ethantruman/cheepy_pi/RP2040_firmware/keyboard_rtos/output_frames/reze_frame_006.png

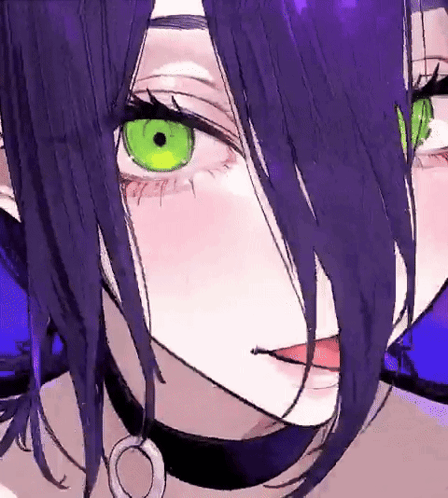
RP2040_firmware/keyboard_rtos/output_frames/reze_frame_006.png
