ethantruman/cheepy_pi/RP2040_firmware/keyboard_rtos/image_data.h

// File tự động tạo bởi Python Script
// Kích thước mỗi ảnh: 71x64 (RGB565 Big-Endian)
#ifndef IMAGE_DATA_H
#define IMAGE_DATA_H

#include <Arduino.h>

#define IMAGE_WIDTH 71
#define IMAGE_HEIGHT 64
#define IMAGE_PIXEL_COUNT 4544
#define TOTAL_IMAGES 6

// Image: reze_frame_001.png
const uint16_t reze_frame_001[4544] PROGMEM = {
    0x414B, 0x416D, 0x392C, 0x412C, 0x416D, 0x496D, 0x518E, 0x518F, 0x496E, 0x59B0, 0x410D, 0x9C54,
    0xFFFF, 0xFF9E, 0xFF9E, 0xFFFF, 0xA4B4, 0x38EB, 0x414C, 0x412C, 0x392C, 0x392C, 0x412D, 0x414D,
    0x496F, 0x494F, 0x6195, 0x81DB, 0x6996, 0x81FB, 0x9A5F, 0x923E, 0x8A1C, 0x925E, 0x925F, 0x923E,
    0x923F, 0x923D, 0x923E, 0x921E, 0x923E, 0x71B7, 0x6174, 0x6996, 0x5972, 0x5151, 0x5151, 0x5151,
    0x59B1, 0x72B1, 0xA476, 0xFFBE, 0xDE7A, 0xFFFF, 0xD5F8, 0x59CE, 0x496F, 0x496F, 0x496E, 0x516F,
    0x498E, 0x414C, 0x414C, 0x496D, 0x496D, 0x498E, 0x414D, 0x414C, 0x414C, 0x414C, 0x414C, 0x414C,
    0x416C, 0x392B, 0x414B, 0x498D, 0x498D, 0x51AF, 0x518F, 0x496E, 0x51AF, 0x496D, 0xDE9B, 0xFFFF,
    0xFFBE, 0xFFBE, 0xFFFF, 0xE6BB, 0x416C, 0x414C, 0x414C, 0x414D, 0x414C, 0x412C, 0x414D, 0x494E,
    0x496F, 0x494F, 0x5973, 0x6175, 0x71B7, 0x923F, 0x923F, 0x81FB, 0x923E, 0x8A1C, 0x71B7, 0x81FC,
    0x8A1C, 0x925E, 0x923E, 0x921D, 0x6996, 0x6174, 0x6174, 0x5972, 0x5171, 0x5151, 0x5151, 0x59D1,
    0x7AB2, 0xB4F7, 0xFFFF, 0xE69A, 0xFFFF, 0xF71C, 0x8332, 0x414D, 0x496E, 0x496E, 0x498E, 0x498E,
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
};

// Mảng chứa con trỏ tới tất cả các ảnh để duyệt vòng lặp for
const uint16_t* const all_images[TOTAL_IMAGES] PROGMEM = {
    reze_frame_001,
    reze_frame_002,
    reze_frame_003,
    reze_frame_004,
    reze_frame_005,
    reze_frame_006,
};

#endif // IMAGE_DATA_H
